multiplanetaryhomestead/reprap-chinampa/design_files/helper-functions.scad

// mirrors object and retains copy of original object
module mirror_copy() {
    children(); // Original object
    mirror(v) children(); // Mirrored object
}

// isometric grid for drain mesh
// implemented as 3x rectilinear grid patterns stacked on top of each other and rotated 60 degrees apart
module isometric_grid_generator(r=30, w=0.8, h_layer=0.2, h_bottom_shell=3*0.2, n=6, d_hole=1.2) {
    n_bottom_shell = h_bottom_shell/h_layer;
    rotate([0, 0, 30])
    for (i = [0:1:n_bottom_shell-1]) {
        translate([0, 0, i*h_layer])
        rotate([0, 0, i*60])
        rectilinear_grid_generator(r=r, w=w, h=h_layer, n=n, d_hole=d_hole);
    }
}

// used for generating isometric grid
module rectilinear_grid_generator(r=30, w=0.8, h=0.2, n=3, d_hole=1.2) {
    difference() {
        rotate([0, 0, 90])
        cylinder(h, r=r, $fn=n);
        mirror_copy()
        for (i = [0: w+d_hole: 2*r]) {
            translate([i, 0, h/2])
            cube([d_hole, 2*r, h], center=true);
        }
    }
}

// for generating drain mesh
module honeycomb_generator(n=5, r_hex=0.8, r_dist=1.6, h=0.2) {
    angle=60;
    for (i = [1:1:6]) {
        if (angle*i % angle == 0 && n > 0) {
            rotate([0, 0, angle*i])
            translate([0, r_dist*n, 0])
            cylinder(r=r_hex, h=h, $fn=6);
        }
        if (n % 2 == 0) {
            rotate([0, 0, angle*i])
            translate([r_dist*n*1.5/sqrt(3), 0, 0])
            cylinder(r=r_hex, h=h, $fn=6);
        }
        if (n % 2 == 0 && n > 3) {
            for (j = [-(n-2):2:(n-2)]) {
                rotate([0, 0, angle*i])
                translate([r_dist*n*1.5/sqrt(3), j*r_dist/2, 0])
                cylinder(r=r_hex, h=h, $fn=6);
            }
        }
        if (n % 2 != 0 && n > 2) {
            for (j = [-(n-2):2:(n-2)]) {
                rotate([0, 0, angle*i])
                translate([r_dist*n*1.5/sqrt(3), j*r_dist/2, 0])
                cylinder(r=r_hex, h=h, $fn=6);
            }
        }
    }
    if (n > 0) {
        honeycomb_generator(n=n-1, r_hex=r_hex, r_dist=r_dist, h=h);
    }
}

// water injection port cavity
module water_injection_port_cavity(r, h) {
    rotate([0, 0, 30])
    cylinder(r=r, h=h, $fn=6);
    for (i = [-1:2:1]) {
        rotate([0, 0, 30*i])
        translate([sqrt(3)*r/2, 0, 0])
        cylinder(r=r, h=h, $fn=6);
    }
}

// water injection port walls
module water_injection_port(r_o, r_i, h) {
    difference() {
        union() {
            rotate([0, 0, 30])
            cylinder(r=r_o, h=h, $fn=6);
            for (i = [-1:2:1]) {
                rotate([0, 0, 30*i])
                translate([sqrt(3)*r_o/4, 0, 0])
                cylinder(r=r_o, h=h, $fn=6);
            }
        }

        // water injection port cavity
        water_injection_port_cavity(r_i, h);
    }
}

// shell used to remove protruding water injection port walls
module invisible_shell(r_o, r_i, h) {
    difference() {
        cylinder(r=r_o, h=h);
        cylinder(r=r_i, h=h);
    }
}

// hexagon function
module hexagon2d(r) {
    polygon(points=[[r, 0], [r/2, r*sqrt(3)/2], [-r/2, r*sqrt(3)/2], [-r, 0], [-r/2, -r*sqrt(3)/2], [r/2, -r*sqrt(3)/2]]);
}

//// fillet functions

// used for circular filleted cutout of outer bottom
module circular_outer_bottom_fillet(r_cyl, r_fil, h_bottom_offset, res) {
    translate([0, 0, -h_bottom_offset])
    difference() {
        cylinder(h=r_fil, r=r_cyl, $fn=res);

        // remove layers that would otherwise print steep overhangs due to fillet
        cylinder(h=h_bottom_offset, r=r_cyl);

        bottomFillet(b=0, r=r_fil, s=200)
        cylinder(h=r_fil, r=r_cyl, $fn=res);
    }
}

// based on work by https://github.com/ademuri/openscad-fillets

function filletDepth(r, d, i) = r * cos(asin(d * i / r));

module topBottomFillet(b = 0, t = 2, r = 1, s = 4, e = 1) {
    if (e == 1) {
        topFilletPeice(t = t, r = r, s = s) children(0);
        bottomFilletPeice(b = b, r = r, s = s) children(0);

        render()
        difference() {
            children(0);

            translate([0, 0, t - r])
            linear_extrude(r + 1)
            offset(delta = 1e5)
            projection()
            children(0);

            translate([0, 0, b - 1])
            linear_extrude(r + 1)
            offset(delta = 1e5)
            projection()
            children(0);

        }
    }
    if (e == 0) children(0);
}

module topFillet(t = 2, r = 1, s = 4, e = 1) {
    if (e == 1) {
        topFilletPeice(t = t, r = r, s = s) children(0);

        render()
        difference() {
            children(0);
            translate([0, 0, t-r])
            linear_extrude(r + 1)
            offset(delta = 1e5)
            projection()
            children(0);
        }
    }
    if (e == 0) children(0);
}

module bottomFillet(b = 0, r = 1, s = 4, e = 1) {
    if (e == 1) {
        bottomFilletPeice(b = b, r = r, s = s) children(0);

        render()
        difference() {
            children(0);
            translate([0, 0, b - 1])
            linear_extrude(r + 1)
            offset(delta = 1e5)
            projection()
            children(0);
        }
    }
    if (e == 0) children(0);
}

module topFilletPeice(t = 2, r = 1, s = 4) {
    d = r/s;

    for (i = [0:s]) {
        x = filletDepth(r, d, i);
        z = d * (s - i + 1);
        translate([0, 0, t - z])
        linear_extrude(d)
        offset(delta = -r + x)
        projection(true)
        translate([0, 0, -t + z])
        children(0);
    }
}

module bottomFilletPeice(b = 0, r =1, s = 4) {
    d = r/s;

    for (i = [0:s]) {
        x = filletDepth(r, d, i);
        z = d * (s - i);
        translate([0, 0, b + z])
        linear_extrude(d)
        offset(delta = -r + x)
        projection(true)
        translate([0, 0, b - z])
        children(0);
    }
}

module rounding2d(r) {
    offset(r = r) offset(delta = -r) children(0);
}
